fouldsy/piper-pa-28-flight-sim/docs/images/inside-sim.jpg

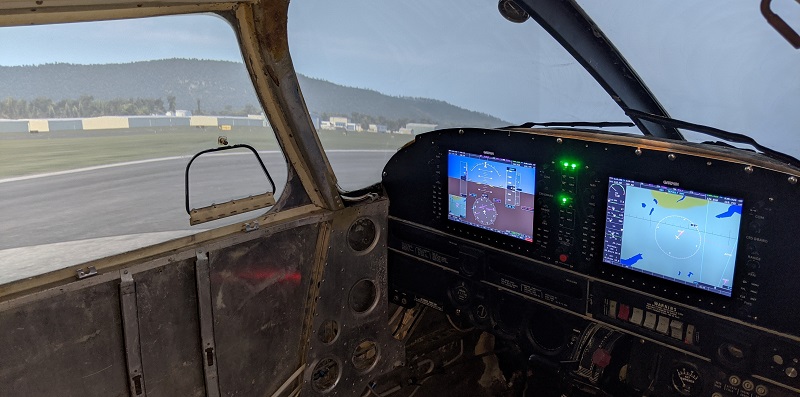
docs/images/inside-sim.jpg
